crehmann/Buzzard/Case/TopPlate/README.MD

# Top Plate

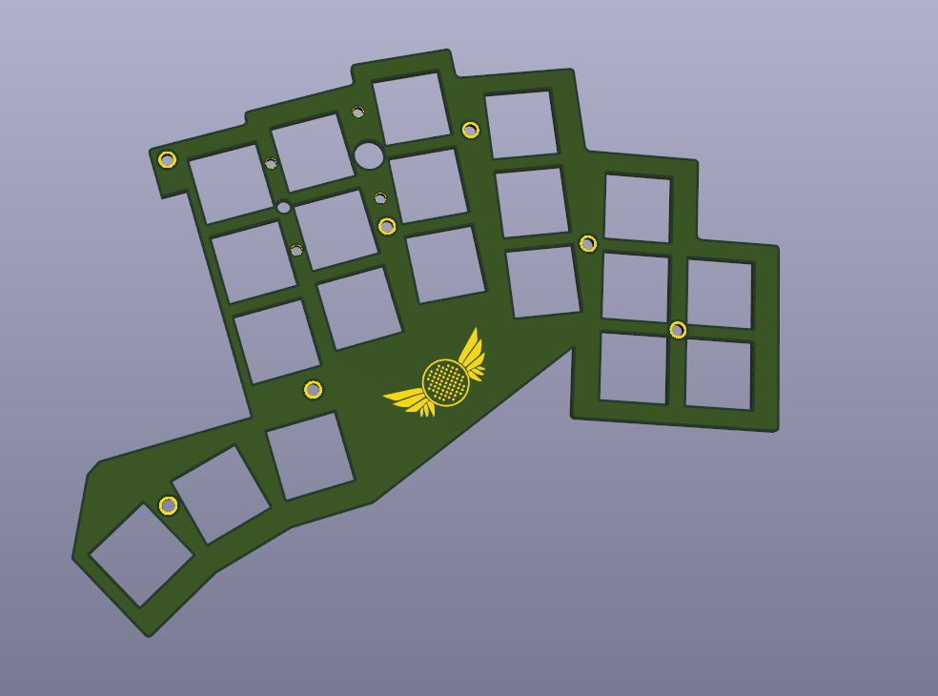
[picture p2: Pictures/TopPlate.png]
Render Image


**Note:** The top and bottom plate are a little bit larger design than the keyboard PCB itself. I am planning to also create a 3d printed border that can be clamped between the top and bottom plate.
