crehmann/Buzzard/Pictures/pcb.PNG

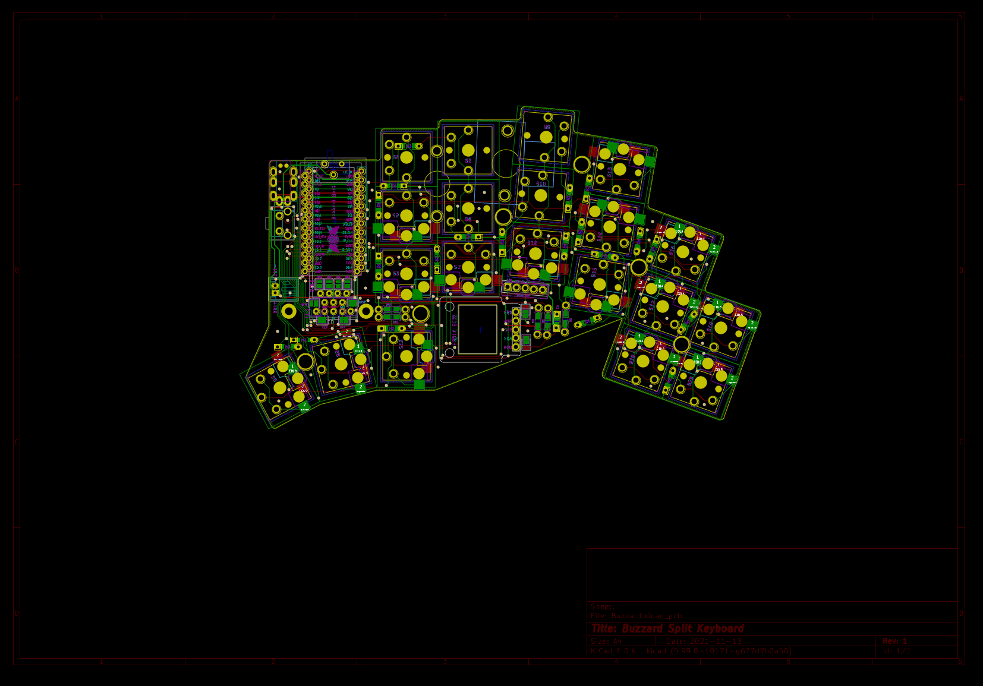
Pictures/pcb.PNG
