crehmann/Buzzard/Pictures/build_guide_final_wireless.jpg

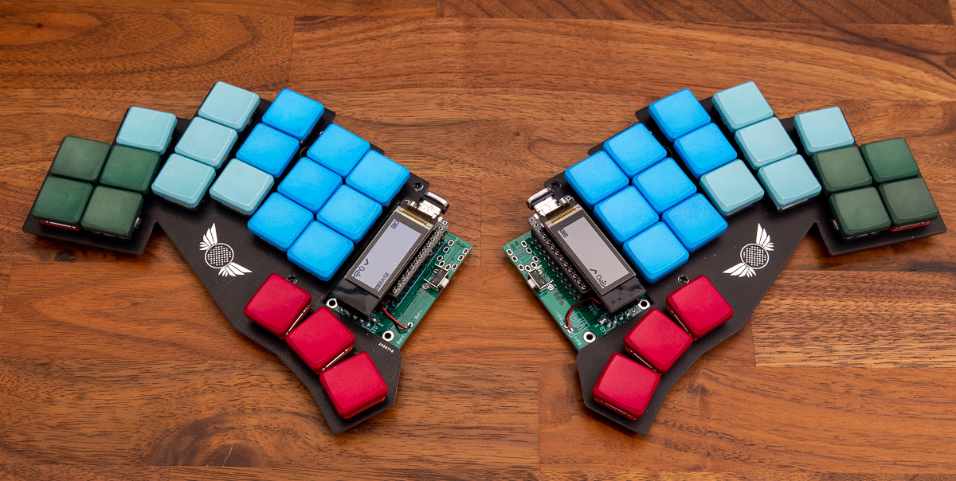
Pictures/build_guide_final_wireless.jpg
