crehmann/Buzzard/Pictures/build_guide_hot_swap.jpg

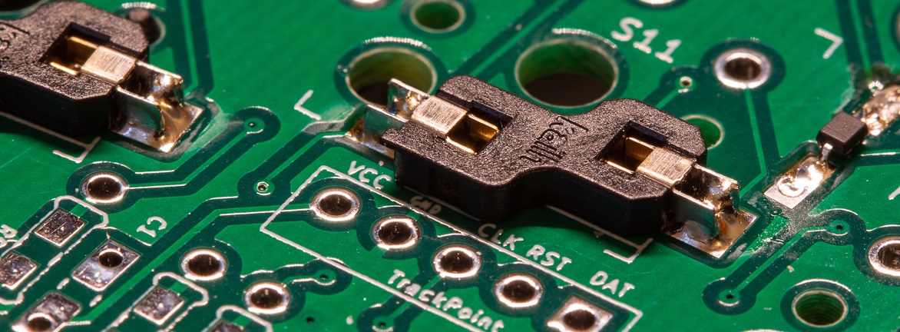
Pictures/build_guide_hot_swap.jpg
