crehmann/Buzzard/Pictures/build_guide_lcd.jpg

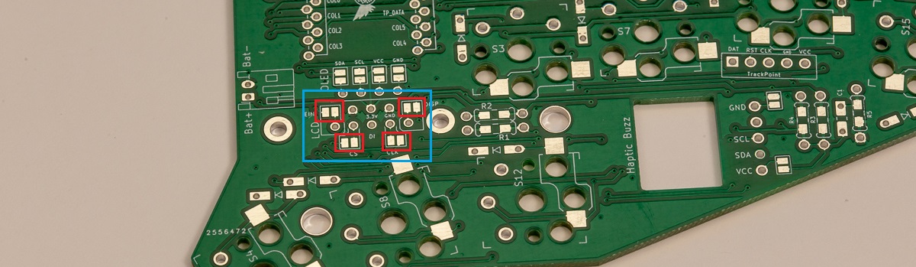
Pictures/build_guide_lcd.jpg
