crehmann/Buzzard/Pictures/build_guide_microcontroller.jpg

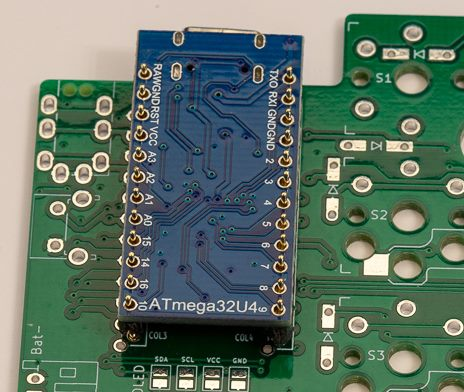
Pictures/build_guide_microcontroller.jpg
