crehmann/Buzzard/Pictures/build_guide_microcontroller_sockets.jpg

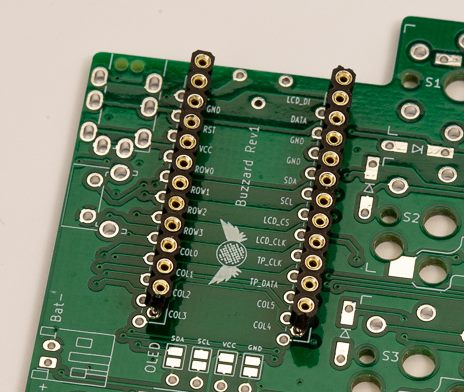
Pictures/build_guide_microcontroller_sockets.jpg
