crehmann/Buzzard/Pictures/build_guide_oled.jpg

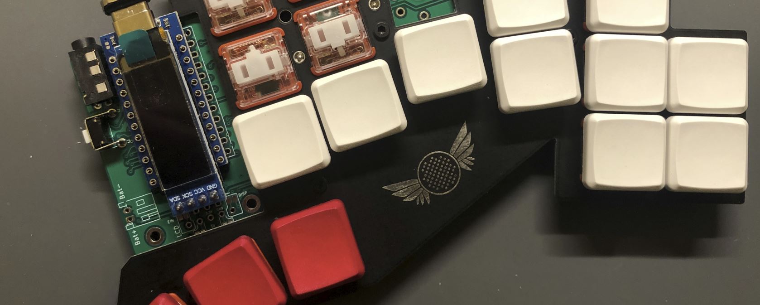
Pictures/build_guide_oled.jpg
