crehmann/Buzzard/Pictures/build_guide_oled_jumpers.jpg

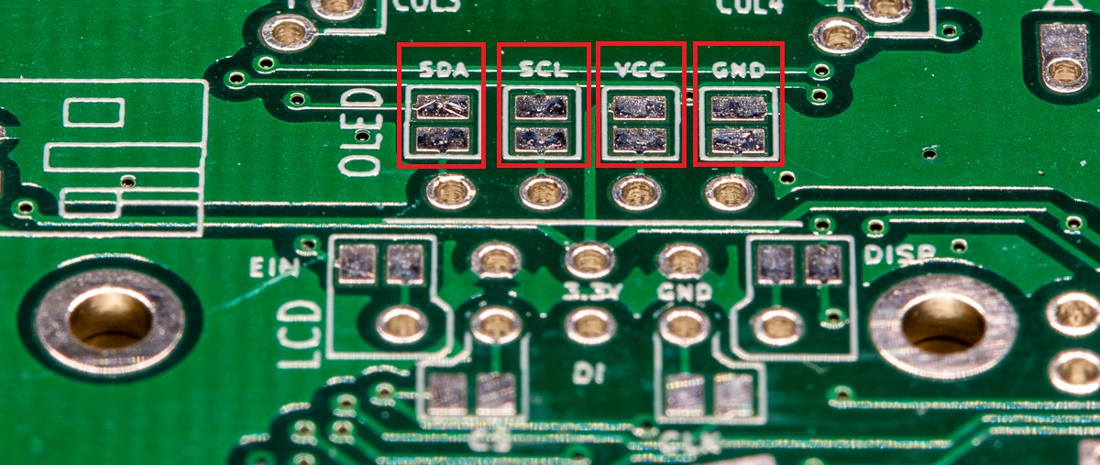
Pictures/build_guide_oled_jumpers.jpg
