crehmann/Buzzard/Pictures/build_guide_pcb_prepare.jpg

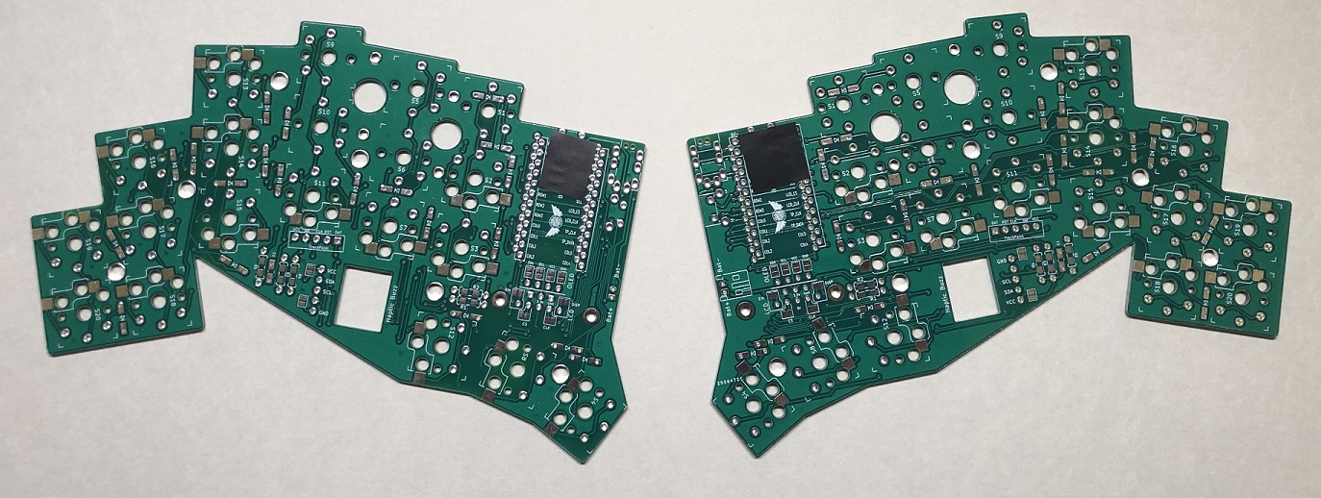
Pictures/build_guide_pcb_prepare.jpg
