crehmann/Buzzard/Pictures/build_guide_switches.jpg

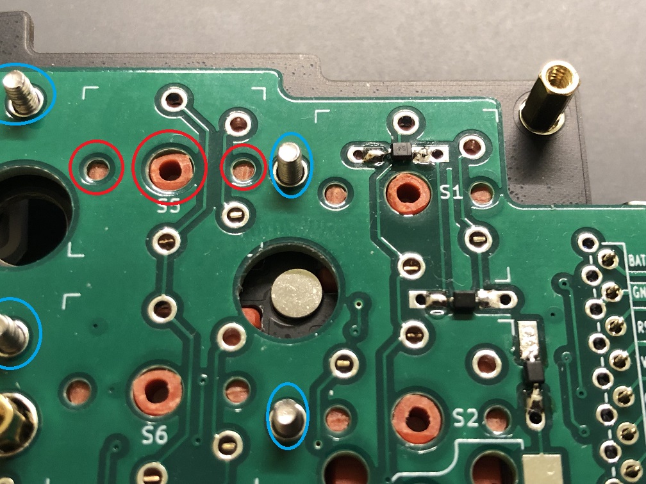
Pictures/build_guide_switches.jpg
