crehmann/Buzzard/Pictures/build_guide_trackpoint_back.png

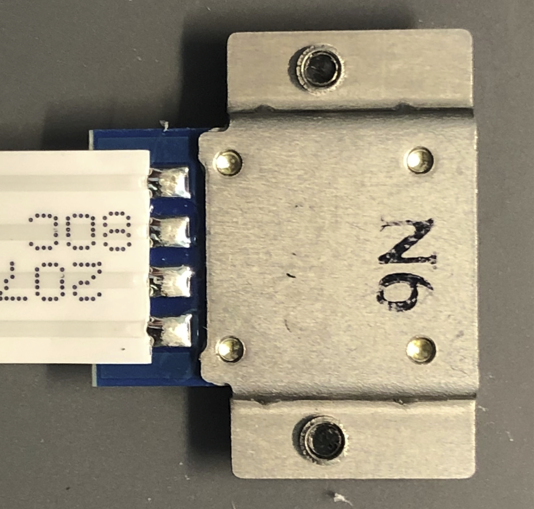
Pictures/build_guide_trackpoint_back.png
