crehmann/Buzzard/Pictures/build_guide_trackpoint_cap.jpg

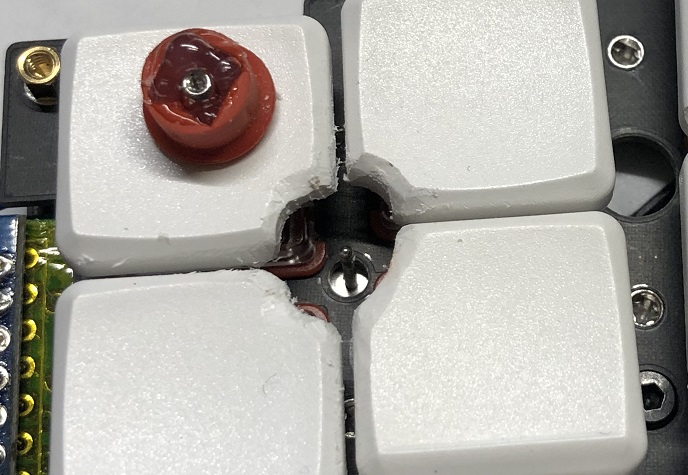
Pictures/build_guide_trackpoint_cap.jpg
