crehmann/Buzzard/Pictures/build_guide_trackpoint_extension.png

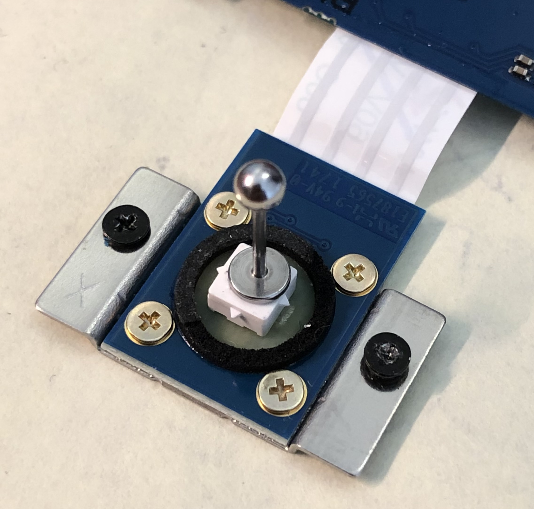
Pictures/build_guide_trackpoint_extension.png
