crehmann/Buzzard/Pictures/build_guide_trackpoint_installed.jpg

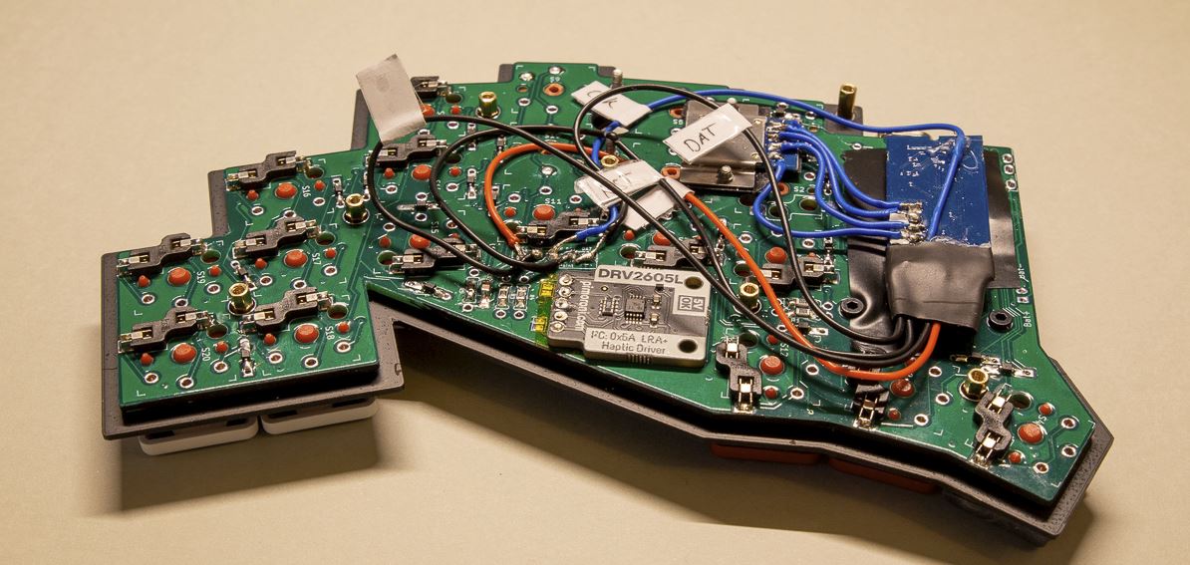
Pictures/build_guide_trackpoint_installed.jpg
