crehmann/Buzzard/Pictures/build_guide_trackpoint_pinout.jpg

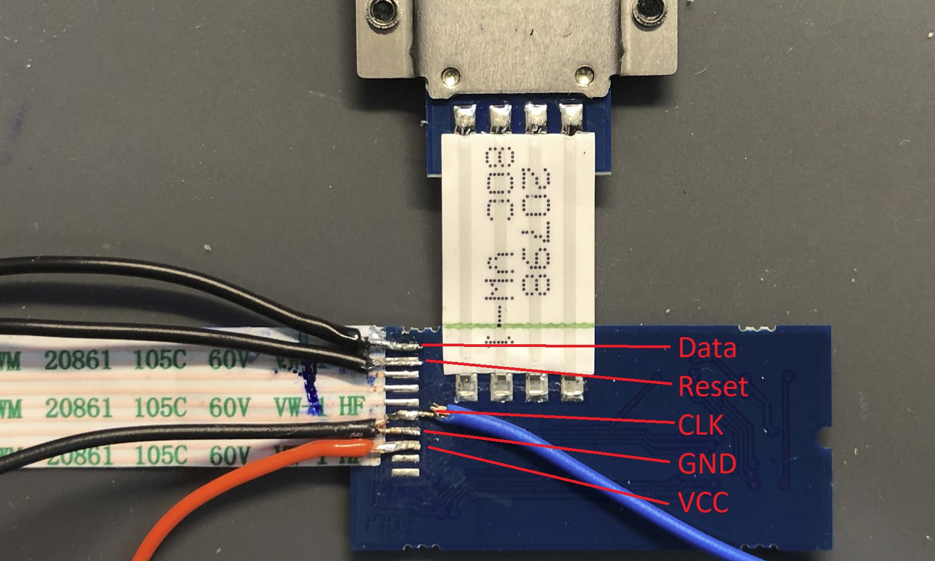
Pictures/build_guide_trackpoint_pinout.jpg
